lithiumice/XTerminal/2.Software/XTerminal-ESP32-firmware/bak_lib/Adafruit ICM20X/assets/649.png

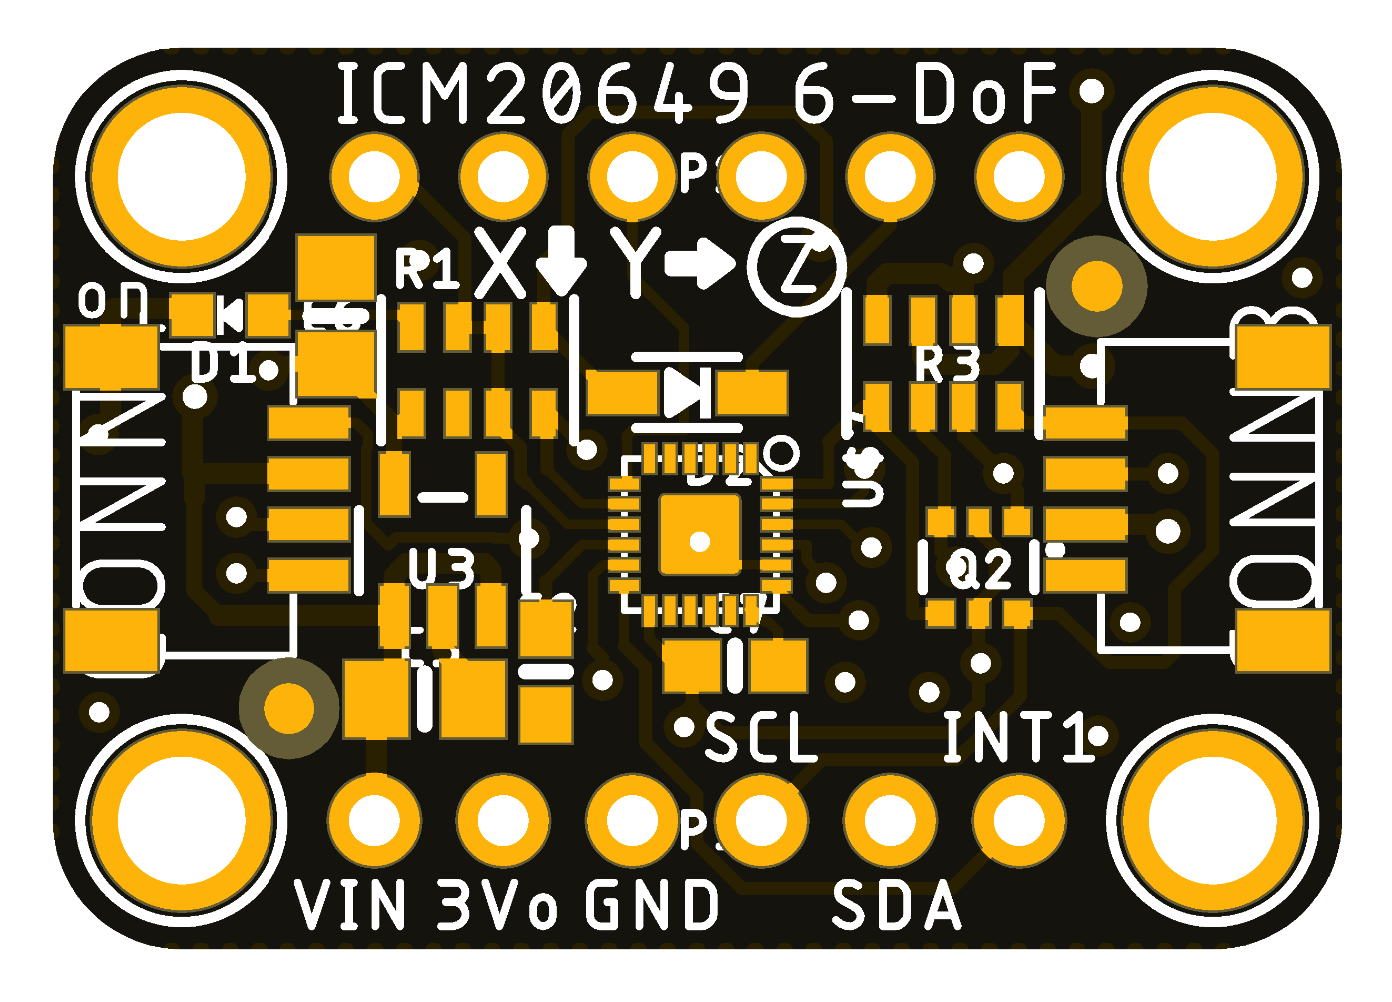
2.Software/XTerminal-ESP32-firmware/bak_lib/Adafruit ICM20X/assets/649.png
