lithiumice/XTerminal/6.DocImages/MP3.jpg

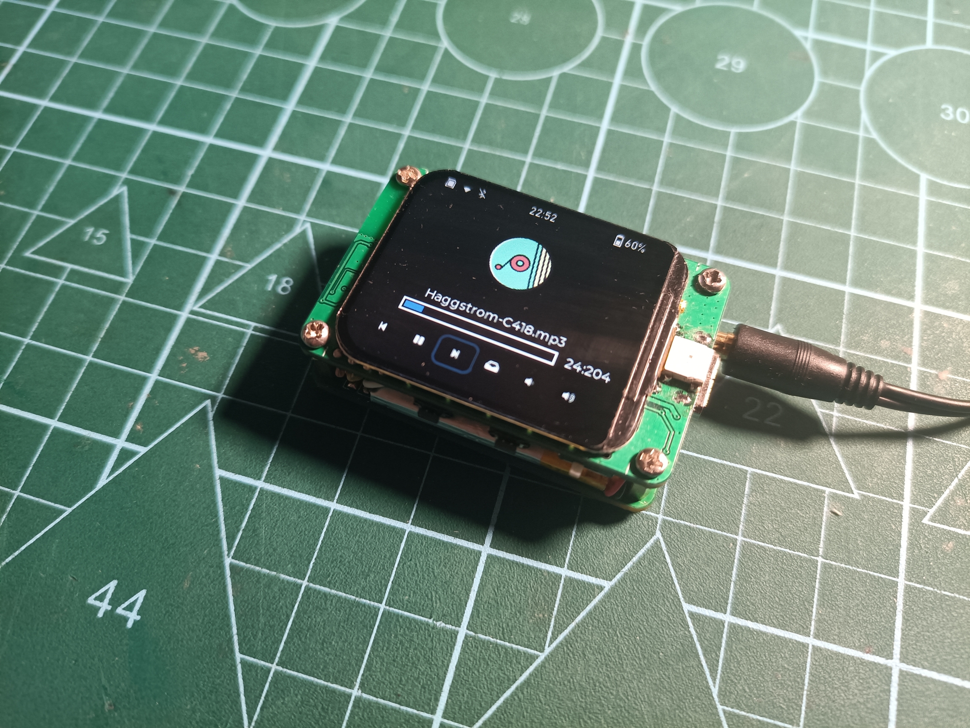
6.DocImages/MP3.jpg
