lithiumice/XTerminal/6.DocImages/主板.jpg

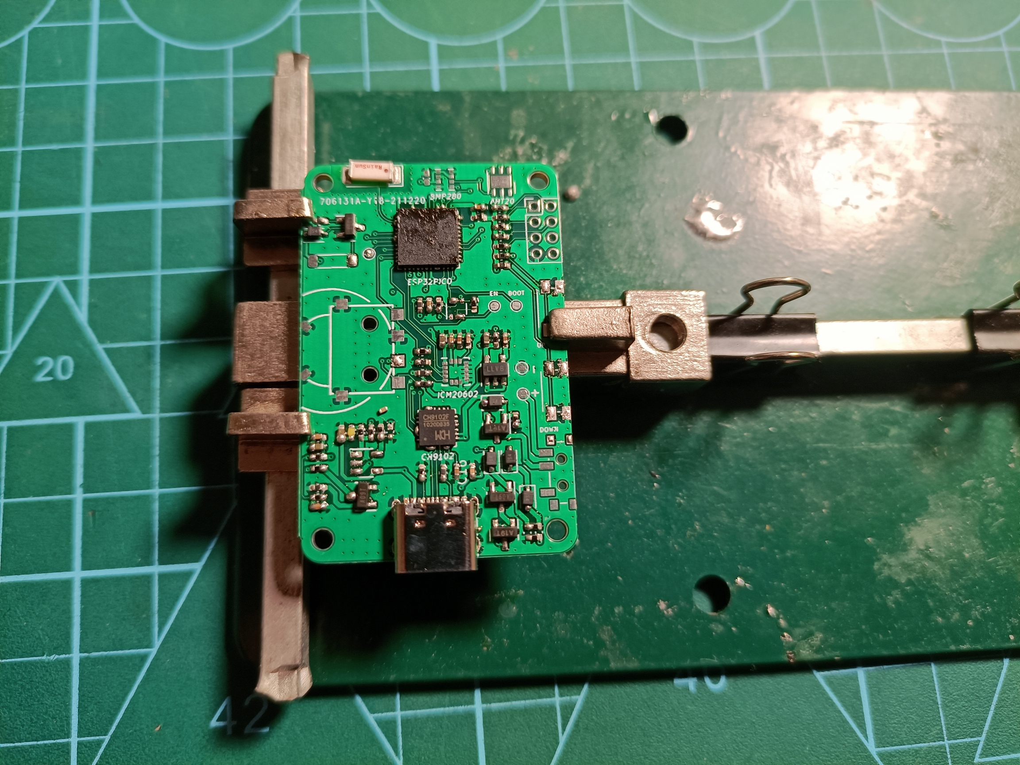
6.DocImages/主板.jpg
