lithiumice/XTerminal/2.Software/XTerminal-ESP32-firmware/bak_lib/lv_100ask_demo_memory/test.png

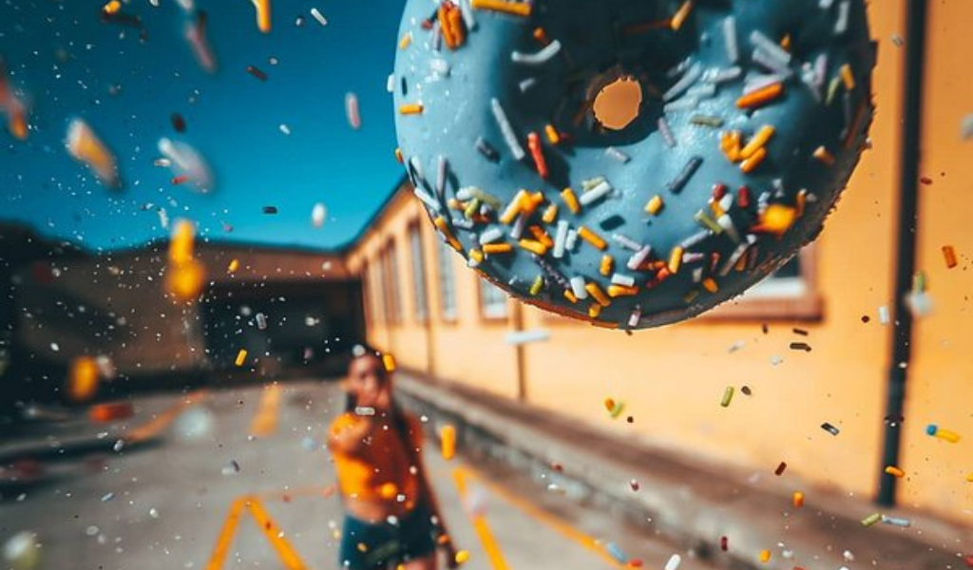
2.Software/XTerminal-ESP32-firmware/bak_lib/lv_100ask_demo_memory/test.png
