lithiumice/XTerminal/6.DocImages/原理图.pdf

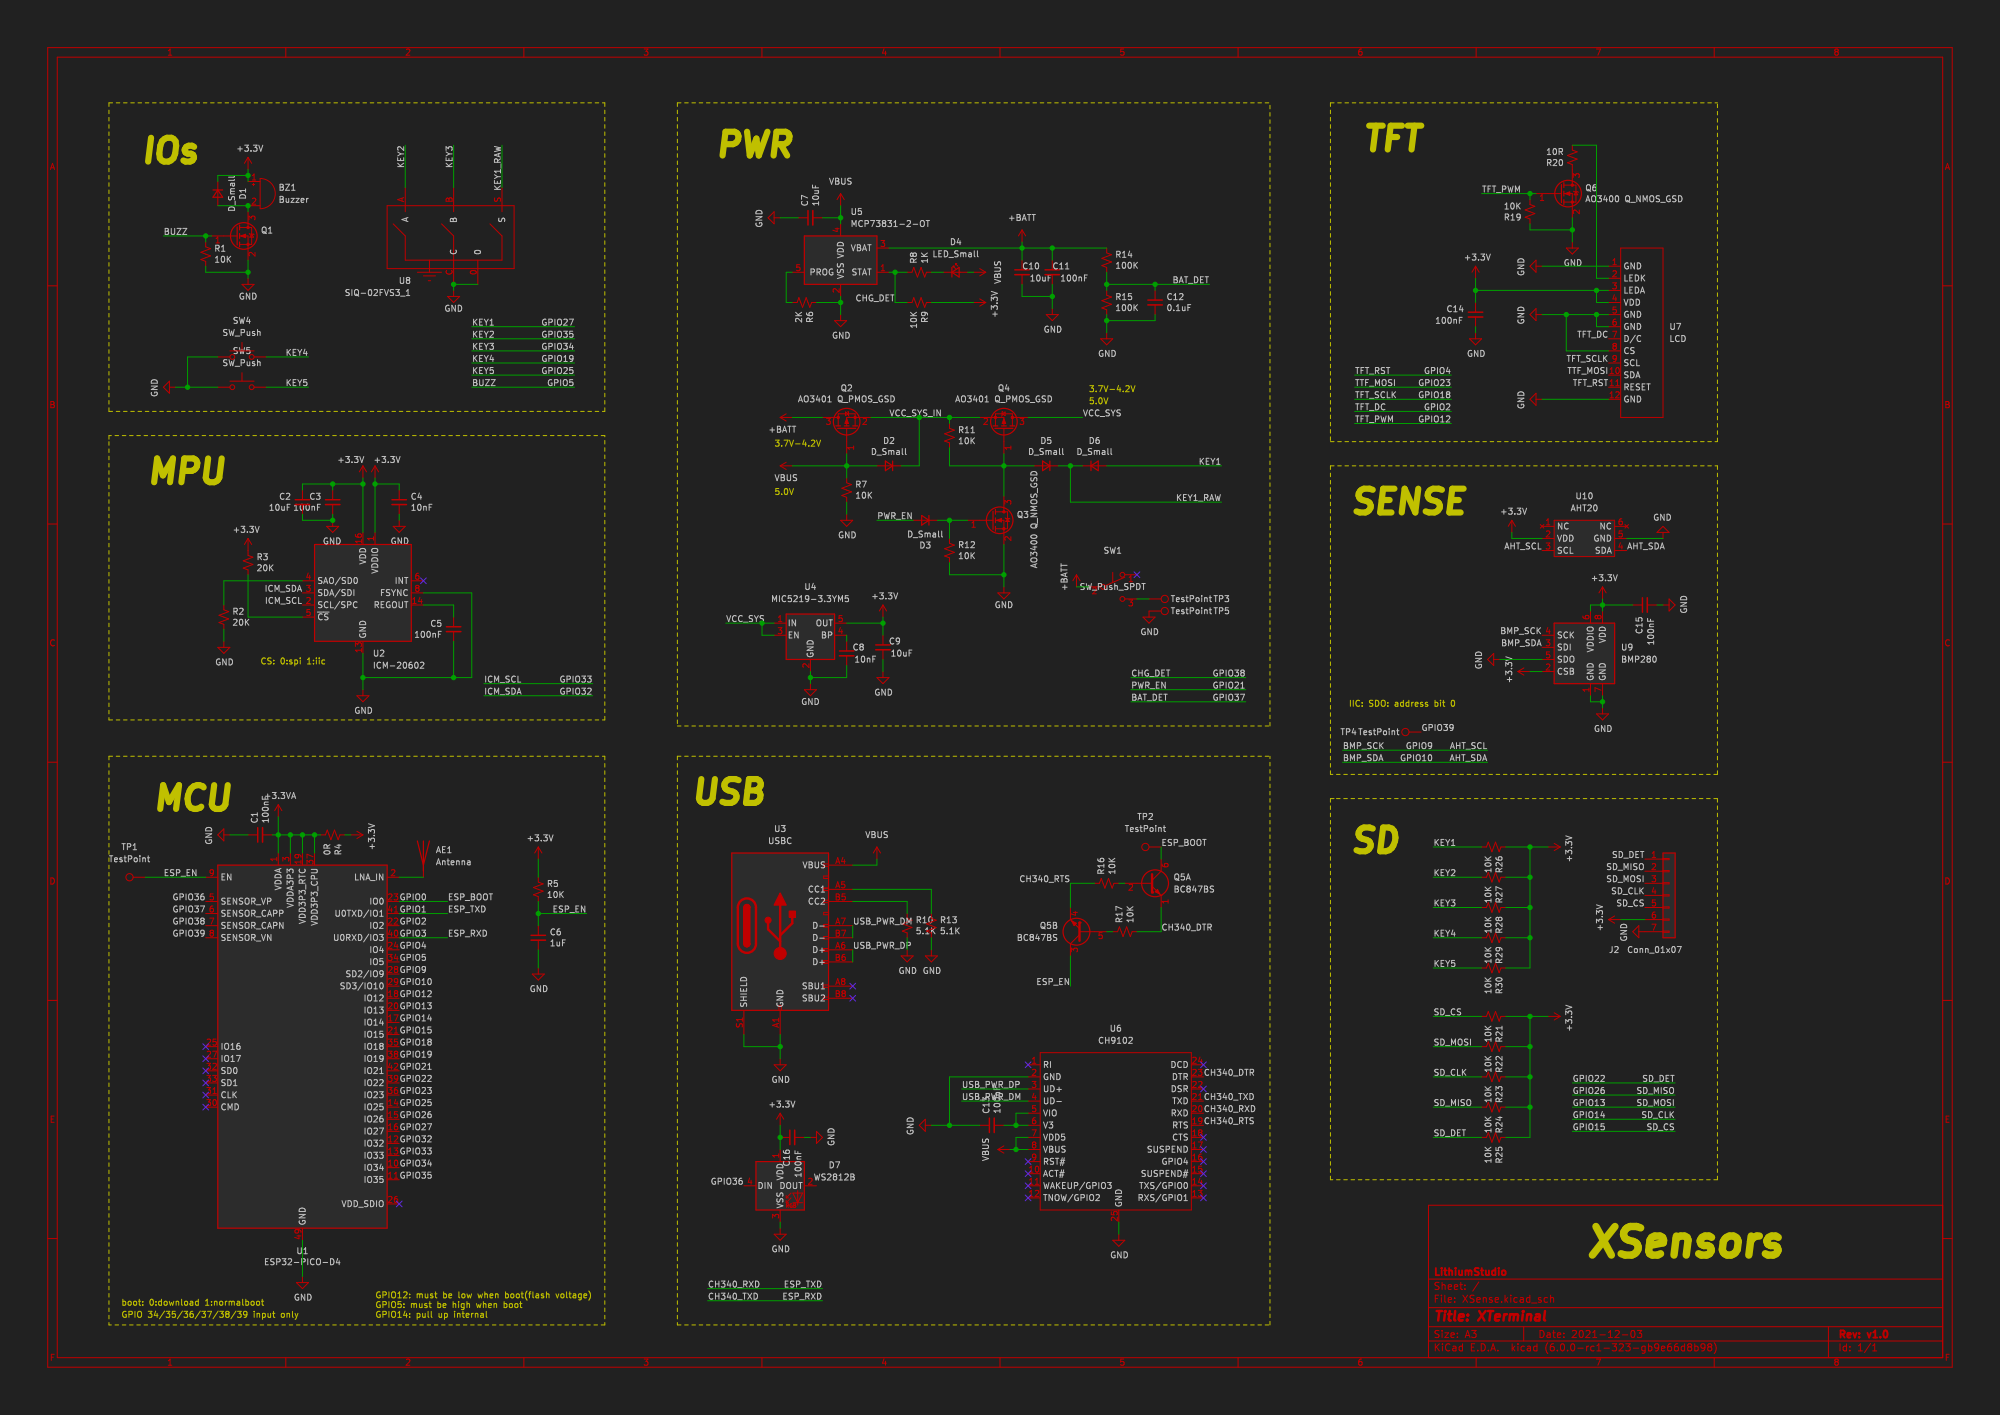
[picture p61: page 1]
