lithiumice/XTerminal/2.Software/XTerminal-ESP32-firmware/src/App/Pages/GameArduboy/Game/GameArduboy3D/Defines.h

#pragma once

#if _WIN32
#include <stdint.h>
#include <string.h>
#define PROGMEM
#define PSTR
#define pgm_read_byte(x) (*((uint8_t*)x))
#define pgm_read_word(x) (*((uint16_t*)x))
#define pgm_read_ptr(x) (*((uintptr_t*)x))
#define strlen_P(x) strlen(x)
#else
// #include <avr/pgmspace.h>
// #include "../ArduinoLib/avr/pgmspace.h"
#ifdef ARDUINO
#include <pgmspace.h>
#else
#include <avr/pgmspace.h>
#endif

#define pgm_read_ptr(x) (*((uintptr_t*)x))
#endif

#ifdef _WIN32
#define DISPLAY_WIDTH 128
#define DISPLAY_HEIGHT 64
#else
#define DISPLAY_WIDTH 128
#define DISPLAY_HEIGHT 64
#endif

#define TARGET_FRAMERATE 30
#define DEV_MODE 0

#define INPUT_LEFT 1
#define INPUT_RIGHT 2
#define INPUT_UP 4
#define INPUT_DOWN 8
#define INPUT_A 16
#define INPUT_B 32

#define COLOUR_WHITE 1
#define COLOUR_BLACK 0

#define FIXED_ANGLE_MAX 256

#define CAMERA_SCALE 1
#define CLIP_PLANE 32
#define CLIP_ANGLE 32
#define NEAR_PLANE_MULTIPLIER 130
#define NEAR_PLANE (DISPLAY_WIDTH * NEAR_PLANE_MULTIPLIER / 256)
#define HORIZON (DISPLAY_HEIGHT / 2)

#define CELL_SIZE 256
#define PARTICLES_PER_SYSTEM 8
#define BASE_SPRITE_SIZE 16
#define MAX_SPRITE_SIZE (DISPLAY_HEIGHT / 2)
#define MIN_TEXTURE_DISTANCE 4
#define MAX_QUEUED_DRAWABLES 12

#define TURN_SPEED 3
