lithiumice/XTerminal/2.Software/XTerminal-ESP32-firmware/src/App/Pages/GameArduboy/GameArduboy.cpp

#include "GameArduboy.h"
#include <ctime>
#include "HAL/HAL.h"
#include <stdio.h>
#include <stdlib.h>
using namespace Page;
#include "Game/GamePrivate.h"
#include "Game/GameDisp.h"
#include "lvgl.h"

#define GAME_DISP_WIDTH 128
#define GAME_DISP_HEIGHT 64
#define BTN_SIZE 48

#define IMPORT_GAME(name)       \
    extern void name##_setup(); \
    extern void name##_loop();

#define REG_GAME(index, name)   \
    extern void name##_setup(); \
    extern void name##_loop();

#include "_GameList.inc"
#undef REG_GAME


// import os
// name='virus'
// a=os.listdir()
// for i in a:
//     if(i[-3:]=='cpp'):
//         os.rename(i,f'{name}_'+i)


static lv_group_t *game_group;
static lv_obj_t *contGameDisp;
static lv_obj_t *canvasGame;
static lv_color_t canvasBuf[LV_CANVAS_BUF_SIZE_INDEXED_1BIT(GAME_DISP_WIDTH, GAME_DISP_HEIGHT)];
static lv_obj_t *contBtnGrp;
static lv_obj_t *btnGrp[GAME_BUTTON_MAX];
uint32_t enc_dir_event_time = 0;
uint8_t enc_btn_down_flag = 0;
uint8_t enc_exit_flag = 0;

static BtnCfg_TypeDef btnCfg[GAME_BUTTON_MAX] =
    {
        {"A", LV_ALIGN_BOTTOM_RIGHT, -20, -70},
        {"B", LV_ALIGN_BOTTOM_RIGHT, -20, -10},
        {"U", LV_ALIGN_TOP_MID, 0, 5},
        {"D", LV_ALIGN_BOTTOM_MID, 0, -5},
        {"L", LV_ALIGN_LEFT_MID, 5, 0},
        {"R", LV_ALIGN_RIGHT_MID, -5, 0},
};
static LED_TypeDef ledGrp[GAME_LED_MAX] =
    {
        {lv_palette_main(LV_PALETTE_RED), -20},
        {lv_palette_main(LV_PALETTE_GREEN), -0},
        {lv_palette_main(LV_PALETTE_BLUE), 20},
};

static void ButtonGrp_EventHandler(lv_event_t *event)
{
    lv_obj_t *obj = lv_event_get_target(event);
    lv_event_code_t code = lv_event_get_code(event);
    auto *instance = (lv_obj_t *)lv_obj_get_user_data(obj);

    for (int i = 0; i < GAME_BUTTON_MAX; i++)
    {
        if (obj == btnGrp[i])
        {
            if (code == LV_EVENT_PRESSED)
            {
                Game_SetButtonState(i, true);
            }
            else if (code == LV_EVENT_RELEASED || code == LV_EVENT_PRESS_LOST)
            {
                Game_SetButtonState(i, false);
            }
        }
    }

//    if (code == LV_EVENT_KEY)
//	{
//		uint32_t key = (*(uint32_t*)event->param);
//		if (key == LV_KEY_LEFT)
//		{
//            Game_SetButtonState(GAME_BUTTON_LEFT, true);
//            enc_btn_down_flag = 1;
//            enc_dir_event_time = millis();
//        }
//        else if (key == LV_KEY_RIGHT)
//		{
//            Game_SetButtonState(GAME_BUTTON_RIGHT, true);
//             enc_btn_down_flag = 1;
//            enc_dir_event_time = millis();
//		}
//	}
}

void Game_Setup()
{
    switch (HAL::game_select_index)
    {
#define REG_GAME(index, name) \
    case index:               \
        name##_setup();       \
        break;

#include "_GameList.inc"
#undef REG_GAME
    }
}

void Game_Loop()
{
    switch (HAL::game_select_index)
    {
#define REG_GAME(index, name) \
    case index:               \
        name##_loop();        \
        break;

#include "_GameList.inc"
#undef REG_GAME
    }
}

void Game_BtnGrp_Create(lv_obj_t *par)
{
    lv_obj_t *contBtn = lv_obj_create(par);
    lv_obj_set_size(contBtn, BTN_SIZE * 3 + 10, BTN_SIZE * 3 + 10);
    lv_obj_set_style_radius(contBtn, 5, 0);
    lv_obj_set_style_border_width(contBtn, 0, 0);
    lv_obj_align(contBtn, LV_ALIGN_BOTTOM_LEFT, 10, 15);
    lv_obj_set_style_bg_color(contBtn, lv_color_black(), 0);
    contBtnGrp = contBtn;

    for (int i = 0; i < GAME_BUTTON_MAX; i++)
    {
        lv_obj_t *btn = lv_btn_create((i >= GAME_BUTTON_UP) ? contBtn : par);
        lv_obj_set_size(btn, BTN_SIZE, BTN_SIZE);
        lv_obj_align(btn, btnCfg[i].align, btnCfg[i].x_mod, btnCfg[i].y_mod);
        lv_obj_set_style_text_font(btn, &lv_font_montserrat_16, 0);
        lv_obj_set_style_bg_color(btn, lv_color_black(), 0);
        lv_obj_set_style_radius(btn, 0, 0);
        lv_obj_set_style_border_color(btn, lv_color_black(), 0);
        lv_obj_set_style_border_width(btn, 0, 0);
        lv_obj_add_event_cb(btn, ButtonGrp_EventHandler, LV_EVENT_ALL, NULL);

        lv_obj_t *label = lv_label_create(btn);
        lv_label_set_text(label, btnCfg[i].sym);
        lv_obj_set_style_text_color(label, lv_color_white(), 0);
        lv_obj_set_opa_scale(btn, LV_OPA_TRANSP);

        btnGrp[i] = btn;
    }
}

void Game_Canvas_Create(lv_obj_t *par)
{
    lv_obj_t *canvas = lv_canvas_create(par);
    lv_canvas_set_buffer(canvas, canvasBuf, GAME_DISP_WIDTH, GAME_DISP_HEIGHT, LV_IMG_CF_INDEXED_1BIT);
    lv_canvas_set_palette(canvas, 0, lv_color_black());
    lv_canvas_set_palette(canvas, 1, lv_color_white());
    lv_obj_align(canvas, LV_ALIGN_CENTER, 0, 0);
    lv_obj_set_scrollbar_mode(canvas, LV_SCROLLBAR_MODE_OFF);
    lv_group_add_obj(game_group, canvas);
    lv_obj_add_event_cb(canvas, ButtonGrp_EventHandler, LV_EVENT_ALL, NULL);

    canvasGame = canvas;
}

void Game_Canvas_DrawBuf(uint8_t *buf, int16_t w, int16_t h)
{
    // #   define IsWhite ((buf[(row*w) + x] & (1 << bit_position)) >> bit_position)
    lv_color_t c;
    lv_obj_t *canvas = canvasGame;
    lv_img_dsc_t *dsc = lv_canvas_get_img(canvas);

    for (int16_t y = 0; y < h; y++)
    {
        for (int16_t x = 0; x < w; x++)
        {
            uint8_t row = y / 8;
            uint8_t bit_position = y % 8;
            c.full = ((buf[(row * w) + x] & (1 << bit_position)) >> bit_position);
            lv_img_buf_set_px_color(dsc, x, y, c);
        }
    }

    lv_obj_invalidate(canvas);
}

void Game_ContDisp_Create(lv_obj_t *par)
{
    lv_obj_t *cont = lv_obj_create(par);
    lv_obj_set_size(cont, GAME_DISP_WIDTH + 4, GAME_DISP_HEIGHT + 4);
    lv_obj_align(cont, LV_ALIGN_TOP_MID, 0, 25);
    lv_obj_set_style_radius(cont, 0, 0);
    lv_obj_set_style_border_color(cont, LV_COLOR_MAKE(0x33, 0x99, 0x99), 0);
    lv_obj_set_scrollbar_mode(cont, LV_SCROLLBAR_MODE_OFF);
    contGameDisp = cont;
    // lv_group_add_obj(game_group,contGameDisp);
}

void Game_LED_Create(lv_obj_t *par)
{
    for (int i = 0; i < GAME_LED_MAX; i++)
    {
        lv_obj_t *led = lv_led_create(par);
        lv_obj_set_style_bg_color(led, ledGrp[i].color, 0);
        lv_obj_set_style_border_width(led, 0, 0);
        lv_obj_set_size(led, 10, 10);
        lv_obj_set_opa_scale(led, LV_OPA_TRANSP);
        lv_obj_align(led, LV_ALIGN_LEFT_MID, ledGrp[i].x_ofs, -10);
        lv_led_off(led);
        ledGrp[i].led = led;
    }
}

void Game_SetLEDState(uint8_t led_id, bool val)
{
    if (led_id < GAME_LED_MAX && ledGrp[led_id].led != NULL)
    {
        lv_obj_t *led = ledGrp[led_id].led;
        val ? lv_led_on(led) : lv_led_off(led);
    }
}

void Game_SetLEDBright(uint8_t led_id, uint8_t val)
{
    if (led_id < GAME_LED_MAX && ledGrp[led_id].led != NULL)
    {
        lv_obj_t *led = ledGrp[led_id].led;
        lv_led_set_brightness(led, val);
    }
}

GameArduboy::GameArduboy()
{
}

GameArduboy::~GameArduboy()
{
}

void GameArduboy::onCustomAttrConfig()
{
    SetCustomCacheEnable(true);
    SetCustomLoadAnimType(PageManager::LOAD_ANIM_OVER_BOTTOM, 500, lv_anim_path_bounce);
}

void GameArduboy::onViewLoad()
{
    // View.Create(root);
    lv_obj_remove_style_all(root);
    lv_obj_set_size(root, LV_HOR_RES, LV_VER_RES);
    StatusBar::SetStyle(StatusBar::STYLE_TRANSP);
    game_group = lv_group_create();

    Game_Setup();
    Game_ContDisp_Create(root);
    Game_LED_Create(root);
    Game_Canvas_Create(contGameDisp);
    Game_BtnGrp_Create(root);
}

void GameArduboy::onViewDidLoad()
{
}

void GameArduboy::onViewWillAppear()
{
    lv_indev_set_group(lv_get_indev(LV_INDEV_TYPE_ENCODER), game_group);
    StatusBar::SetStyle(StatusBar::STYLE_TRANSP);

    lv_obj_set_style_bg_color(root, lv_color_white(), LV_PART_MAIN);

    timer = lv_timer_create(onTimerUpdate, 10, this);
    lv_timer_ready(timer);

    lv_obj_fade_in(root, 300, 0);

    // HAL::Encoder_SetEnable(false);
}

void GameArduboy::onViewDidAppear()
{
    // lv_group_focus_obj(View.ui.canvas);
}

void GameArduboy::onViewWillDisappear()
{
    lv_obj_fade_out(root, 300, 0);
}

void GameArduboy::onViewDidDisappear()
{
    lv_timer_del(timer);
    // HAL::Encoder_SetEnable(true);
}

void GameArduboy::onViewDidUnload()
{
    // View.Delete();
    // Model.DeInit();
}

void GameArduboy::AttachEvent(lv_obj_t *obj)
{
    lv_obj_set_user_data(obj, this);
    lv_obj_add_event_cb(obj, onEvent, LV_EVENT_ALL, this);
}
#include "HAL/HAL_IMU.h"

void GameArduboy::Update()
{
    Game_Loop();
    Game_DispTaskUpdate();

    if (enc_btn_down_flag == 1 &&
        millis() - enc_dir_event_time > 200)
    {
        enc_btn_down_flag = 0;
        Game_ClearButtonState();
    }

    if (gflag.enc_long_push_flag == 1)
    {
        gflag.enc_long_push_flag = 0;
        Manager->Pop();
    }
}

void GameArduboy::onTimerUpdate(lv_timer_t *timer)
{
    GameArduboy *instance = (GameArduboy *)timer->user_data;
    instance->Update();
}

void GameArduboy::onEvent(lv_event_t *event)
{
    lv_obj_t *obj = lv_event_get_target(event);
    lv_event_code_t code = lv_event_get_code(event);
    auto *instance = (GameArduboy *)lv_obj_get_user_data(obj);

}
