lithiumice/XTerminal/2.Software/XTerminal-ESP32-firmware/bak_lib/Game/chribocchi/game.cpp

#include "common.h"
#include "lvgl_port.h"
#include <random>

/*  Defines  */

#define BOXES   128
#ifdef DEBUG
#define SNOWS   16
#else
#define SNOWS   64
#endif

enum {
    STATE_START = 0,
    STATE_GAME,
    STATE_OVER,
    STATE_PAUSE,
};

enum {
    ALIGN_LEFT = 0,
    ALIGN_CENTER,
    ALIGN_RIGHT,
};

#define coord(x)        ((x) * 64)
#define coordInv(x)     ((x) / 64)
#define secs(s)         ((s) * 60)
#define mid(a, b, c)    max(min((b), (c)), (a))
#define sign(n)         (((n) > 0) - ((n) < 0))

/*  Typedefs  */

typedef struct {
    int16_t x, y;
    int8_t  vx, vy;
} BOX;

typedef struct {
    int8_t x, y;
} SNOW;

/*  Local Functions  */

static void startGame(void);
static void moveCat(void);
static void initBoxes(void);
static void throwFirstBox(void);
static void moveBoxes(void);
static void boundBox(BOX *pBox, int gap);
static int  getNewBoxIndex(void);
static void initSnows(void);
static void moveSnows(void);

static void drawCat(void);
static void drawSantaClaus(void);
static void drawBoxes(void);
static void drawSnows(void);
static void drawStrings(void);
static int  drawFigure(int16_t x, int16_t y, int value, uint8_t align);

/*  Local Variables  */

PROGMEM static const uint8_t imgBox[6][8] = { // 8x8 x6
    { 0x7E, 0x99, 0x99, 0xFF, 0xFF, 0x99, 0x99, 0x7E },
    { 0x7E, 0x8D, 0xC9, 0xF9, 0x9F, 0x93, 0xB1, 0x7E },
    { 0x7C, 0x47, 0xED, 0xB9, 0x9D, 0xB7, 0xE2, 0x3E },
    { 0x3C, 0x66, 0xE7, 0x99, 0x99, 0xE7, 0x66, 0x3C },
    { 0x3E, 0xE2, 0xB7, 0x9D, 0xB9, 0xED, 0x47, 0x7C },
    { 0x7E, 0xB1, 0x93, 0x9F, 0xF9, 0xC9, 0x8D, 0x7E },
};

PROGMEM static const uint8_t imgCat[8][48] = { // 24x12 x8
    {
        0x7C, 0xFE, 0xC7, 0xFE, 0xFC, 0xC6, 0xFF, 0xFE, 0xFC, 0xC0, 0xC0, 0xE0, 0xE0, 0xE0, 0xE0, 0xE0,
        0xE0, 0xC0, 0xC0, 0x80, 0xC0, 0x62, 0x32, 0x1C, 0x00, 0x00, 0x00, 0x01, 0x01, 0x03, 0x0F, 0x0F,
        0x03, 0x03, 0x0F, 0x0F, 0x03, 0x03, 0x03, 0x03, 0x0F, 0x0F, 0x03, 0x03, 0x0F, 0x0F, 0x00, 0x00
    },{
        0x7C, 0xFE, 0xC7, 0xFE, 0xFC, 0xC6, 0xFF, 0xFE, 0xFC, 0xC0, 0xC0, 0xE0, 0xE0, 0xE0, 0xE0, 0xE0,
        0xE0, 0xC0, 0xC0, 0x80, 0xC0, 0xC0, 0x62, 0x3C, 0x00, 0x00, 0x00, 0x01, 0x01, 0x03, 0x03, 0x0F,
        0x0F, 0x03, 0x03, 0x0F, 0x0F, 0x03, 0x03, 0x07, 0x07, 0x03, 0x03, 0x07, 0x07, 0x03, 0x00, 0x00
    },{
        0x7C, 0xFE, 0xC7, 0xFE, 0xFC, 0xC6, 0xFF, 0xFE, 0xFC, 0xC0, 0xC0, 0xE0, 0xE0, 0xE0, 0xE0, 0xE0,
        0xE0, 0xC0, 0xC0, 0x80, 0x80, 0x00, 0x80, 0xF8, 0x00, 0x00, 0x00, 0x01, 0x01, 0x03, 0x03, 0x03,
        0x0F, 0x0F, 0x03, 0x0F, 0x0F, 0x03, 0x0F, 0x0F, 0x03, 0x03, 0x0F, 0x0F, 0x03, 0x01, 0x01, 0x00
    },{
        0x7C, 0xFE, 0xDF, 0xFE, 0xFC, 0xDE, 0xFF, 0xFE, 0xFC, 0xC0, 0xC0, 0xE0, 0xE0, 0xE0, 0xE0, 0xE0,
        0xE0, 0xC0, 0xC0, 0x80, 0xC0, 0xC0, 0x62, 0x3C, 0x00, 0x00, 0x00, 0x01, 0x01, 0x03, 0x03, 0x07,
        0x07, 0x03, 0x03, 0x07, 0x07, 0x03, 0x03, 0x0F, 0x0F, 0x03, 0x03, 0x0F, 0x0F, 0x03, 0x00, 0x00
    },{
        0x1C, 0x32, 0x62, 0xC0, 0x80, 0xC0, 0xC0, 0xE0, 0xE0, 0xE0, 0xE0, 0xE0, 0xE0, 0xC0, 0xC0, 0xFC,
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

    /*  In case of pausing  */
    if (state == STATE_PAUSE) {
        if (arduboy.buttonDown(A_BUTTON | B_BUTTON)) {
            state = STATE_GAME;
            ignoreCnt = 30; // a half second
            toDraw = true;
            dprintln("Resume");
        }
        return false;
    }

    /*  Usual case  */
    moveCat();
    moveBoxes();
    if (SNOWS - boxCnt > 0) moveSnows();
    counter--;
    if (state == STATE_START) {
        if (counter == secs(1)) {
            throwFirstBox();
        } else if (counter == 0) {
            state = STATE_GAME;
        }
    } else if (state == STATE_GAME) {
        if (timer > 0) timer--;
        gameFrames++;
        if (boxCnt == 0) {
            state = STATE_OVER;
            isHiscore = (setLastScore(score, gameFrames) == 0);
            counter = secs(8);
            arduboy.playScore2(soundOver, 1);
            dprint("Game Over: score=");
            dprintln(score);
        } else if (ignoreCnt == 0 && arduboy.buttonDown(A_BUTTON | B_BUTTON)) {
            state = STATE_PAUSE;
            dprintln("Pause");
        }
    } else if (state == STATE_OVER) {
        if (ignoreCnt == 0 && arduboy.buttonDown(A_BUTTON | B_BUTTON)) {
            startGame();
        }
    }
    if (ignoreCnt > 0) ignoreCnt--;
    toDraw = true;

    return (state == STATE_OVER && counter == 0);
}

void drawGame(void)
{
    if (toDraw) {
        if (boxCnt >= BOXES / 3 && state == STATE_GAME && counter % 2 == 0) {
            return; // Frame skip
        }
        arduboy.clear();
        arduboy.drawFastVLine2(0, 0, 64, WHITE);
        arduboy.drawFastVLine2(127, 0, 64, WHITE);
        drawSnows();
        if (state != STATE_PAUSE) drawBoxes();
        drawCat();
        if (state == STATE_START) drawSantaClaus();
        drawStrings();
        toDraw = false;
    }
}

/*---------------------------------------------------------------------------*/
/*                             Control Functions                             */
/*---------------------------------------------------------------------------*/

static void startGame()
{
    state = STATE_START;
    gameFrames = 0;
    counter = secs(2);
    timer = 5 * secs(60); // 2 minutes
    score = 0;
    arduboy.playScore2(soundStart, 0);
    dprintln("Start Game");
}

static void moveCat(void)
{
    int vx = 0;
    if (state == STATE_START) {
        vx = sign(64 - catX);
        catX += vx;
    } else {
        if (arduboy.buttonPressed(LEFT_BUTTON)) vx--;
        if (arduboy.buttonPressed(RIGHT_BUTTON)) vx++;
        catX = mid(0, catX + vx, 128);
    }

    if (vx != 0) {
        catAnim = ((catAnim & 0xF) + 1) & 0xF;
        if (vx > 0) catAnim |= 0x10;
    } else {
        catAnim &= 0x10;
    }

    if (meowY > 0) {
        meowY--;
    } else if (0 && arduboy.buttonDown(DOWN_BUTTON)) {
        meowY = 8;
        arduboy.playScore2(soundMeow, 2);
        dprintln("meow");
    }
}

static void initBoxes(void)
{
    for (int i = 0; i < BOXES; i++) {
        boxAry[i].x = -1;
    }
    boxCnt = 0;
    boxIdx = 0;
}

static void throwFirstBox(void)
{
    BOX *pBox = &boxAry[0];
    pBox->x = coord(64);
    pBox->y = coord(32);
    pBox->vx = 0;
    pBox->vy = -64;
    boxCnt = 1;
}

static void moveBoxes(void)
{
    boolean isBound = false;
    for (int i = 0; i < BOXES; i++) {
        BOX *pBox = &boxAry[i];
        if (pBox->x < 0) continue;
        uint16_t lastY = pBox->y;
        pBox->x += pBox->vx;
        pBox->y += pBox->vy;
        pBox->vy++;

        if (pBox->x < coord(4)) {
            pBox->x = coord(4);
            pBox->vx = -pBox->vx * 3 / 4;
        } else if (pBox->x > coord(124)) {
            pBox->x = coord(124);
            pBox->vx = -pBox->vx * 3 / 4;
        }

        int gap = pBox->x - coord(catX);
        if (timer > 0 && pBox->y >= coord(60) && lastY < coord(60) && abs(gap) <= coord(10)) {
            boundBox(pBox, coordInv(gap));
            isBound = true;
            score++;
        } else if (pBox->y > coord(70)) {
            pBox->x = -1;
            boxCnt--;
        }
    }

    if (isBound) {
        arduboy.tunes.tone((timer > secs(30)) ? 1440 : 1920, 15);
        dprint("boxCnt=");
        dprintln(boxCnt);
    }
}

static void boundBox(BOX *pBox, int gap)
{
    int16_t x = pBox->x;
    int8_t  vx = pBox->vx;
    int8_t  vy = -pBox->vy / 2;

    int mul = 2;
    if (timer > secs(30)) {
        mul = 2;
        gap -= 4;
    } else {
        mul = 3;
        gap -= 8;
    }
    for (int i = 0; i < mul; i++, gap += 8) {
        if (i > 0 && boxCnt < BOXES) {
            pBox = &boxAry[getNewBoxIndex()];
            pBox->x = x;
            boxCnt++;
        }
        pBox->y = coord(60);
        pBox->vx = vx + gap;
        pBox->vy = vy - (40 - abs(gap));
    }
}

static int getNewBoxIndex(void)
{
    do {
        boxIdx = (boxIdx + 1) % BOXES;
    } while (boxAry[boxIdx].x >= 0);
    return boxIdx;
}
long random(long howbig)
{
    if (howbig == 0)
    {
        return 0;
    }
    return rand() % howbig;
}
long random(long howsmall, long howbig)
{
    if (howsmall >= howbig)
    {
        return howsmall;
    }
    long diff = howbig - howsmall;
    return random(diff) + howsmall;
}

static void initSnows(void)
{
    for (int i = 0; i < SNOWS; i++) {
        SNOW *pSnow = &snowAry[i];
        pSnow->x = random(128);
        pSnow->y = random(64);
    }
}

static void moveSnows(void)
{
    for (int i = 0; i < SNOWS; i++) {
        SNOW *pSnow = &snowAry[i];
        pSnow->x += random(-1, 2);
        pSnow->y += random(2);
        if (pSnow->y >= 64) {
            pSnow->x = random(128);
            pSnow->y = 0;
        }
    }
}

/*---------------------------------------------------------------------------*/
/*                              Draw Functions                               */
/*---------------------------------------------------------------------------*/

static void drawCat(void)
{
    if (meowY > 0) {
        arduboy.printEx(catX - 12, 46 + meowY / 2, F("MEOW"));
    }
    arduboy.fillRect2(catX - 12 + (catAnim & 0x10), 55, 8, 3, BLACK);
    arduboy.drawBitmap(catX - 12, 52, imgCat[catAnim / 4], 24, 12, WHITE);
}

static void drawSantaClaus(void)
{
    arduboy.drawBitmap(counter * 2 - 112, 16, imgSantaClaus, 64, 32, WHITE);
}

static void drawBoxes(void)
{
    for (int i = 0; i < BOXES; i++) {
        BOX *pBox = &boxAry[i];
        if (pBox->x < 0) continue;
        int16_t x = coordInv(pBox->x) - 4;
        int16_t y = coordInv(pBox->y) - 4;
        int8_t anim = x % 6;
        arduboy.drawBitmap(x, y, imgBox[anim], 8, 8, WHITE);
    }
}

static void drawSnows(void)
{
    for (int i = 0, c = SNOWS - boxCnt; i < c; i++) {
        SNOW *pSnow = &snowAry[i];
        arduboy.drawPixel(pSnow->x, pSnow->y, WHITE);
    }
}

static void drawStrings(void)
{
    if (state == STATE_START) {
        arduboy.drawBitmap(36, 0, imgReady, 56, 19, WHITE);
    } else {
        /*  Score  */
        drawFigure(2, 0, score, ALIGN_LEFT);

        /*  Timer  */
        if (timer >= secs(60)) {
            drawFigure(92, 0, timer / 3600, ALIGN_LEFT);
            arduboy.drawBitmap(102, 0, imgDash, 4, 4, WHITE);
            drawFigure(116, 0, timer % 3600 / 60, ALIGN_RIGHT);
        } else {
            drawFigure(98, 0, timer / 60, ALIGN_RIGHT);
            arduboy.drawBitmap(108, 0, imgDash, 8, 4, WHITE);
            drawFigure(116, 0, timer % 60 / 6, ALIGN_LEFT);
        }
        if (state == STATE_GAME) {
            if (timer <= secs(30) && timer > secs(27)) {
                arduboy.drawBitmap(38, 16, imgFever, 52, 14, (timer % 8 < 4) ? WHITE : BLACK);
            }
        } else if (state == STATE_OVER) {
            int y = 12;
            if (counter > 458) {
                y -= (counter - 458) * 2;
            } else if (counter > secs(7)) {
                y += counter % 2;
            }
            arduboy.drawBitmap(0, y, imgOver, 128, 32, WHITE);
            if (isHiscore && counter % 8 < 4) {
                arduboy.printEx(31, 46, F("NEW RECORD!"));
            }
        } else if (state == STATE_PAUSE) {
            arduboy.printEx(49, 46, F("PAUSE"));
        }
    }
}

static int  drawFigure(int16_t x, int16_t y, int value, uint8_t align)
{
    int k = (value > 9) ? drawFigure(x - align * 5, y, value / 10, align) : 0;
    arduboy.drawBitmap(x + k, y, imgFigures[value % 10], 10, 14, WHITE);
    return k + 10 - align * 5;
}
