lithiumice/XTerminal/2.Software/XTerminal-ESP32-firmware/bak_lib/Game/chribocchi/title.cpp

#include <cstdlib>

#include "common.h"
#include <App/Pages/Game/Arduboy2/Arduboy2Core.h>

/*  Defines  */

enum {
    STATE_MENU = 0,
    STATE_RECORD,
    STATE_CREDIT,
};

enum {
    MENU_START = 0,
    MENU_SOUND,
    MENU_RECORD,
    MENU_CREDIT,
};

enum {
    RECORD_NOT_READ = 0,
    RECORD_INITIAL,
    RECORD_STORED,
};

#define EEPROM_ADDR_BASE    832
#define EEPROM_SIGNATURE    0x034E424FUL // "OBN\x03"

/*  Typedefs  */

typedef struct
{
    const uint8_t *pImg;
    uint8_t width;
} TITLE_LETTER;

/*  Local Functions  */

static bool handleButtons(void);
static void setSound(bool enabled);
static void playSound1(void);
static void playSound2(void);
static void readRecord(void);

static void drawTitleMenu(void);
static void drawTitleRecord(void);
static void drawTitleCredit(void);

/*  Local Variables  */

PROGMEM static const uint8_t imgTitle1[192] = { // 96x16
    0x00, 0x00, 0x00, 0x00, 0x00, 0x00, 0x00, 0x00, 0x00, 0x00, 0x00, 0x80, 0x80, 0x80, 0xC0, 0x40,
    0xA0, 0x60, 0xA0, 0x50, 0xB0, 0x50, 0xB0, 0x50, 0xA0, 0x60, 0xA0, 0x40, 0xC0, 0x00, 0x80, 0x80,
    0x80, 0xE0, 0xFE, 0xFF, 0xFF, 0xFF, 0xFC, 0xF0, 0xC0, 0xC0, 0xC0, 0xC0, 0xC0, 0xC0, 0xC0, 0xE0,
    0xF8, 0xFE, 0xFE, 0xFE, 0xFC, 0xF0, 0x80, 0x80, 0xC0, 0xC0, 0xC0, 0xE0, 0xE0, 0xC0, 0xC0, 0x80,
    0x00, 0x02, 0x86, 0xFC, 0x78, 0x00, 0x00, 0x00, 0x00, 0x00, 0x00, 0x00, 0x00, 0x00, 0x00, 0x80,
    0x80, 0x80, 0x80, 0x80, 0x80, 0x40, 0x40, 0x40, 0x40, 0x40, 0x40, 0x20, 0x20, 0x20, 0x00, 0x00,
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
    0x00, 0x00, 0x00, 0x00, 0x00, 0x00, 0x00, 0x00, 0x00, 0x00, 0x00, 0x00, 0x07, 0xFD, 0xAA, 0x55,
    0xBE, 0x7F, 0xBE, 0x1D, 0x82, 0x55, 0xAA, 0x55, 0xAA, 0x55, 0xAA, 0x55, 0xAA, 0x55, 0xAA, 0x00
};

PROGMEM static const char menuText[] = "START GAME\0SOUND \0RECORD\0CREDIT";
PROGMEM static const char creditText[] = "- " APP_TITLE " -\0\0" APP_RELEASED \
        "\0PROGREMMED BY OBONO\0\0THIS PROGRAM IS\0" "RELEASED UNDER\0" "THE MIT LICENSE.";

static uint8_t  state;
static bool     toDraw;
static bool     sound;
static int8_t   menuPos;
static uint16_t lastScore = 0;
static uint8_t  recordState = RECORD_NOT_READ;
static uint16_t hiScore[10];
static uint16_t playCount;
static uint32_t playFrames;

/*---------------------------------------------------------------------------*/
/*                              Main Functions                               */
/*---------------------------------------------------------------------------*/

void initTitle(void)
{
    state = STATE_MENU;
    menuPos = MENU_START;
    toDraw = true;
    setSound(arduboy.audio.enabled());
    if (recordState == RECORD_NOT_READ) {
        readRecord();
    }
}
void randomSeed(unsigned long seed);
bool updateTitle(void)
{
    bool ret = false;
    if (state == STATE_MENU) {
        ret = handleButtons();
    } else {
        if (arduboy.buttonDown(A_BUTTON | B_BUTTON)) {
            state = STATE_MENU;
            playSound2();
            toDraw = true;
        }
    }

#ifdef DEBUG
    if (dbgRecvChar == 'r') {
        arduboy.eepSeek(EEPROM_ADDR_BASE);
        for (int i = 0; i < 8; i++) {
            arduboy.eepWrite32(0);
        }
        recordState = RECORD_INITIAL;
        dprintln("Clean EEPROM");
    }
#endif

    randomSeed(rand() ^ millis()); // Shuffle random
    return ret;
}

void drawTitle(void)
{
    if (toDraw) {
        arduboy.clear();
        switch (state) {
        case STATE_MENU:
            drawTitleMenu();
            break;
        case STATE_RECORD:
            drawTitleRecord();
            break;
        case STATE_CREDIT:
            drawTitleCredit();
            break;
        }
        toDraw = false;
    }
}

uint8_t setLastScore(int score, uint32_t frames)
{
    lastScore = score;

    /*  Updarte best 10  */
    int r = 10;
    uint16_t h;
    while (r > 0 && (h = hiScore[r - 1]) < score) {
        if (--r < 9) hiScore[r + 1] = h;
    }
    if (r < 10) hiScore[r] = score;
    playCount++;
    playFrames += frames;

    /*  Store record to EEPROM  */
    if (recordState == RECORD_INITIAL) {
        arduboy.eepSeek(EEPROM_ADDR_BASE);
        arduboy.eepWrite32(EEPROM_SIGNATURE);
    }
    arduboy.eepSeek(EEPROM_ADDR_BASE + 4 + r * 2);
    for (int i = r; i < 10; i++) {
        arduboy.eepWrite16(hiScore[i]);
    }
    arduboy.eepWrite16(playCount);
    arduboy.eepWrite32(playFrames);

    uint16_t checkSum = (EEPROM_SIGNATURE & 0xFFFF) + (EEPROM_SIGNATURE >> 16) * 2;
    for (int i = 0; i < 10; i++) {
        checkSum += hiScore[i] * (i + 3);
    }
    checkSum += playCount * 13;
    checkSum += (playFrames & 0xFFFF) * 14 + (playFrames >> 16) * 15;
    arduboy.eepWrite16(checkSum);

    recordState = RECORD_STORED;
    return r;
}

/*---------------------------------------------------------------------------*/
/*                             Control Functions                             */
/*---------------------------------------------------------------------------*/

static bool handleButtons()
{
    bool ret = false;
    if (arduboy.buttonDown(UP_BUTTON)) {
        if (menuPos-- == MENU_START) menuPos = MENU_CREDIT;
        playSound1();
        toDraw = true;
    }
    if (arduboy.buttonDown(DOWN_BUTTON)) {
        if (menuPos++ == MENU_CREDIT) menuPos = MENU_START;
        playSound1();
        toDraw = true;
    }
    if (arduboy.buttonDown(A_BUTTON | B_BUTTON)) {
        switch (menuPos) {
        case MENU_START:
            ret = true;
            arduboy.audio.saveOnOff();
            break;
        case MENU_SOUND:
            setSound(!sound);
            playSound2();
            break;
        case MENU_RECORD:
            state = STATE_RECORD;
            playSound2();
            break;
        case MENU_CREDIT:
            state = STATE_CREDIT;
            playSound2();
            break;
        }
        toDraw = true;
    }
    return ret;
}

static void setSound(bool enabled)
{
    if (enabled) {
        arduboy.audio.on();
    } else {
        arduboy.audio.off();
    }
    sound = enabled;
}

static void playSound1(void)
{
    arduboy.tunes.tone(440, 10);
}

static void playSound2(void)
{
    arduboy.tunes.tone(587, 20);
}

static void readRecord(void)
{
    bool isRegular = false;
    arduboy.eepSeek(EEPROM_ADDR_BASE);
    if (arduboy.eepRead32() == EEPROM_SIGNATURE) {
        uint16_t checkSum = (EEPROM_SIGNATURE & 0xFFFF) + (EEPROM_SIGNATURE >> 16) * 2;
        for (int i = 0; i < 13; i++) {
            checkSum += arduboy.eepRead16() * (i + 3);
        }
        isRegular = (arduboy.eepRead16() == checkSum);
    }

    if (isRegular) {
        /*  Read record from EEPROM  */
        arduboy.eepSeek(EEPROM_ADDR_BASE + 4);
        for (int i = 0; i < 10; i++) {
            hiScore[i] = arduboy.eepRead16();
        }
        playCount = arduboy.eepRead16();
        playFrames = arduboy.eepRead32();
        recordState = RECORD_STORED;
    } else {
        /*  Initialize record  */
        for (int i = 0; i < 10; i++) {
            hiScore[i] = 0;
        }
        playCount = 0;
        playFrames = 0;
        recordState = RECORD_INITIAL;
    }
}

/*---------------------------------------------------------------------------*/
/*                              Draw Functions                               */
/*---------------------------------------------------------------------------*/
#define (arduboy.print) print
#include "stdio.h"
static void drawTitleMenu(void)
{
    /*  Title image  */
    arduboy.drawBitmap(32, 0, imgTitle1, 96, 16, WHITE);
    arduboy.drawBitmap(8, 16, imgTitle2, 112, 16, WHITE);
    arduboy.drawBitmap(0, 32, imgTitle3, 56, 32, WHITE);

    /*  Last score  */
    if (lastScore > 0) {
        arduboy.setCursor(0, 0);
        arduboy.print(lastScore);
    }

    /*  Menu items  */
    char buf[12];
    const char *p = menuText;
    for (int i = 0; i < 4; i++) {
        strcpy(buf, p);
        p += arduboy.printEx(68 - (i == menuPos) * 4, i * 6 + 40, buf) + 1;
        if (i == MENU_SOUND) {
            arduboy.print((sound) ? F("ON") : F("OFF"));
        }
    }
    arduboy.fillRect2(56, menuPos * 6 + 40, 5, 5, WHITE);
}

static void drawTitleRecord(void)
{
    arduboy.printEx(22, 4, F("BEST 10 SCORES"));
    arduboy.drawFastHLine2(0, 12, 128, WHITE);
    for (int i = 0; i < 2; i++) {
        for (int j = 0; j < 5; j++) {
            int r = i * 5 + j;
            arduboy.printEx(i * 60 + 4 - (r == 9) * 6, j * 6 + 14, F("["));
            arduboy.print(r + 1);
            arduboy.print(F("] "));
            arduboy.print(hiScore[r]);
        }
    }
    arduboy.drawFastHLine2(0, 44, 128, WHITE);
    arduboy.printEx(16, 48, F("PLAY COUNT "));
    arduboy.print(playCount);
    arduboy.printEx(16, 54, F("PLAY TIME  "));
    arduboy.print(playFrames / 3600); // minutes
    char buf[6];
    sprintf(buf, "'%02d\"", playFrames / 60 % 60); // seconds
    arduboy.print(buf);
}

static void drawTitleCredit(void)
{
    char buf[20];
    const char *p = creditText;
    for (int i = 0; i < 8; i++) {
        strcpy_P(buf, p);
        uint8_t len = strlen(buf);//, sizeof(buf));
        p += arduboy.printEx(64 - len * 3, i * 6 + 8, buf) + 1;
    }
}
