lithiumice/XTerminal/2.Software/XTerminal-ESP32-firmware/src/App/Pages/GameArduboy/Game/GameMYBL/bitmaps.h

// #ifndef BITMAPS_H
// #define BITMAPS_H
#pragma once


///////////////// Menu bitmaps ////////////////////
///////////////////////////////////////////////////
const unsigned char PROGMEM T_arg[] =
{
  // width, height
  60, 56,
  // ########          ########################         ####    #
  // #######                ##############               ##  ##
  // #######  ########                          #######  ## ####
  // ######   #      #######               ######     #   # ####
  // ######  ##  ###      ##################       ## ##  #  ##
  // ######  #  ####      ##                       ##  #  ##    #
  // ######  #  ####      ##                           #  #######
  // #####   #  ###       ##                           #   #####
  // #####  ##            ##                           ##  ######
  // #####  ##########    ##                            #  ##  ##
  // #####  ################                            #  ##  ##
  // ####   #        #######                            #   #####
  // ####  ##                                           ##  #####
  // ####  #                                             #  #####
  // ####  #                                             #  #####
  // ###   #                                         ##  #   ####
  // ###  ## ##                                      ##  ##  ####
  // ###  #  ##                                           #  ####
  // ###  #                                               #  ####
  // ###  #################                ################  ####
  // ####  ################                ###############   ####
  // ####  ################                ########## ####  #####
  // #####  ###############                ##############  ######
  // #####  ###############                ######  ### ##  ###  #
  // ######  #############                  #####  #####  ###   #
  // ######  #############                  ############  ###  ##
  // #######             #                  #            ########
  // ################### # ############   ### ###################
  // ################### # ############# ###################### #
  // ##########        ###           ######         #############
  // #########          ###           ####           ######   ###
  // ########            ##            ###           ###### # ###
  // ########            ##     ##     ##     ###    ######   ###
  // ########     ###    ##     ###    ##    ####################
  // ########     ###    ##     ###   ###    ###      ###########
  // ########            ##          ####     ##      ###########
  // ########           ######        ######        #############
  // ########           #    #  #     #    #        #    ### ####
  // ########     ###   #    #  ##    #    #        #    ########
  // ########     ###   #    #  ###   #    #        #    ########
  // ########################################################  ##
  // ################  ## ####### ####  ##### #  ############  ##
  // #############  #  #                      #  ################
  // #############  #  #                      #  ################
  // ################  #       ########       #  ################
  // ####   #########  #  ##################  #  #####  #########
  // ###  #  ########  ########################  ####    ########
  // ##  ###  ########  ######################  #####    ########
  // #  #####  #######  ######################  ######  #########
  //   #  ####  #######  ####################  ###  #############
  //  ##  ##### #######  ####################  ###  #############
  //   #######  ##   ###  ##################  ###################
  // #  ### #  ### # ###  ####          ####  ###################
  // ##  ###  ####   ####      ########      ####################
  // ###  #  ########## #########  ##############################
  // ####   #####################  ## ###########################

  0x00, 0x00, 0x00, 0x00, 0x00, 0x80, 0xF8, 0xFE, 0x0F, 0xE3, 0xFB, 0x1B, 0x0B, 0x0B, 0x8B, 0xFB, 0xF3, 0xF7, 0xF6, 0xF6, 0xF6, 0x06, 0x06, 0xEC, 0xEC, 0xEC, 0xEC, 0xEC, 0xEC, 0xEC, 0xEC, 0xEC, 0xEC, 0xEC, 0xEC, 0xEC, 0xEC, 0xEE, 0xE6, 0xF6, 0xF6, 0xF6, 0xF7, 0xF3, 0xFB, 0xFB, 0xCB, 0xCB, 0xFB, 0xE3, 0x0F, 0xFE, 0xF8, 0x80, 0x1E, 0x33, 0x21, 0x21, 0x33, 0x9E,
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
  level16, level17, level18, level19, level20, level21, level22,
  level23, level24, level25, level26, level27, level28, level29,
  level30, /*level31,*/ jace, level32, level33, level35, level34, level36, level39, level37, levelNarrowWalls, level38,
  level40, 
};

// #endif
